PanBabinicz/ghost-feather/modules/sensor/bmi270/bmi270.h

#ifndef _BMI270_H
#define _BMI270_H

#include <stdint.h>

#ifdef __cplusplus
extern "C" {
#endif  /* __cplusplus */

///
/// \brief The BMI270 registers definition.
///
#define BMI270_REG_CHIP_ID                  (0x00)  /*!< Chip identification code.                          */
#define BMI270_REG_ERR_REG                  (0x02)  /*!< Reports sensor error condition.                    */
#define BMI270_REG_STATUS                   (0x03)  /*!< Sensor status flags.                               */
#define BMI270_REG_DATA_0                   (0x04)  /*!< AUX_X(LSB).                                        */
#define BMI270_REG_DATA_1                   (0x05)  /*!< AUX_X(MSB).                                        */
#define BMI270_REG_DATA_2                   (0x06)  /*!< AUX_Y(LSB).                                        */
#define BMI270_REG_DATA_3                   (0x07)  /*!< AUX_Y(MSB).                                        */
#define BMI270_REG_DATA_4                   (0x08)  /*!< AUX_Z(LSB).                                        */
#define BMI270_REG_DATA_5                   (0x09)  /*!< AUX_Z(MSB).                                        */
#define BMI270_REG_DATA_6                   (0x0a)  /*!< AUX_R(LSB).                                        */
#define BMI270_REG_DATA_7                   (0x0b)  /*!< AUX_R(MSB).                                        */
#define BMI270_REG_DATA_8                   (0x0c)  /*!< ACC_X(LSB).                                        */
#define BMI270_REG_DATA_9                   (0x0d)  /*!< ACC_X(MSB).                                        */
#define BMI270_REG_DATA_10                  (0x0e)  /*!< ACC_Y(LSB).                                        */
#define BMI270_REG_DATA_11                  (0x0f)  /*!< ACC_Y(MSB).                                        */
#define BMI270_REG_DATA_12                  (0x10)  /*!< ACC_Z(LSB).                                        */
#define BMI270_REG_DATA_13                  (0x11)  /*!< ACC_Z(MSB).                                        */
#define BMI270_REG_DATA_14                  (0x12)  /*!< GYR_X(LSB).                                        */
#define BMI270_REG_DATA_15                  (0x13)  /*!< GYR_X(MSB).                                        */
#define BMI270_REG_DATA_16                  (0x14)  /*!< GYR_Y(LSB).                                        */
#define BMI270_REG_DATA_17                  (0x15)  /*!< GYR_Y(MSB).                                        */
#define BMI270_REG_DATA_18                  (0x16)  /*!< GYR_Z(LSB).                                        */
#define BMI270_REG_DATA_19                  (0x17)  /*!< GYR_Z(MSB).                                        */
#define BMI270_REG_SENSORTIME_0             (0x18)  /*!< Sensor time <7:0>.                                 */
#define BMI270_REG_SENSORTIME_1             (0x19)  /*!< Sensor time <15:8>.                                */
#define BMI270_REG_SENSORTIME_2             (0x1a)  /*!< Sensor time <23:16>.                               */
#define BMI270_REG_EVENT                    (0x1b)  /*!< Sensor event flags.                                */
#define BMI270_REG_INT_STATUS_0             (0x1c)  /*!< Interrupt/Feature status.                          */
#define BMI270_REG_INT_STATUS_1             (0x1d)  /*!< Interrupt status 1.                                */
#define BMI270_REG_SC_OUT_0                 (0x1e)  /*!< Step counting value byte-0.                        */
#define BMI270_REG_SC_OUT_1                 (0x1f)  /*!< Step counting value byte-1.                        */
#define BMI270_REG_WR_GEST_ACT              (0x20)  /*!< Wrist gesture and activity detection output.       */
#define BMI270_REG_INST                     (0x21)  /*!< Error bits and messge indicating internal status.  */
#define BMI270_REG_TEMPERATURE_0            (0x22)  /*!< Temperature (LSB).                                 */
#define BMI270_REG_TEMPERATURE_1            (0x23)  /*!< Temperature (MSB).                                 */
#define BMI270_REG_FIFO_LENGTH_0            (0x24)  /*!< FIFO byte count register (LSB).                    */
#define BMI270_REG_FIFO_LENGTH_1            (0x25)  /*!< FIFO byte count register (MSB).                    */
#define BMI270_REG_FIFO_DATA                (0x26)  /*!< FIFO data output register.                         */
#define BMI270_REG_FEAT_PAGE                (0x2f)  /*!< Feature config/output page selector.               */
#define BMI270_REG_FEATURES_0               (0x30)  /*!< Input register for feature configuration.          */
#define BMI270_REG_FEATURES_1               (0x31)  /*!< Input register for feature configuration.          */
#define BMI270_REG_FEATURES_2               (0x32)  /*!< Input register for feature configuration.          */
#define BMI270_REG_FEATURES_3               (0x33)  /*!< Input register for feature configuration.          */
#define BMI270_REG_FEATURES_4               (0x34)  /*!< Input register for feature configuration.          */
#define BMI270_REG_FEATURES_5               (0x35)  /*!< Input register for feature configuration.          */
#define BMI270_REG_FEATURES_6               (0x36)  /*!< Input register for feature configuration.          */
#define BMI270_REG_FEATURES_7               (0x37)  /*!< Input register for feature configuration.          */
#define BMI270_REG_FEATURES_8               (0x38)  /*!< Input register for feature configuration.          */
#define BMI270_REG_FEATURES_9               (0x39)  /*!< Input register for feature configuration.          */
#define BMI270_REG_FEATURES_10              (0x3a)  /*!< Input register for feature configuration.          */
#define BMI270_REG_FEATURES_11              (0x3b)  /*!< Input register for feature configuration.          */
#define BMI270_REG_FEATURES_12              (0x3c)  /*!< Input register for feature configuration.          */
#define BMI270_REG_FEATURES_13              (0x3d)  /*!< Input register for feature configuration.          */
#define BMI270_REG_FEATURES_14              (0x3e)  /*!< Input register for feature configuration.          */
#define BMI270_REG_FEATURES_15              (0x3f)  /*!< Input register for feature configuration.          */
#define BMI270_REG_ACC_CONF                 (0x40)  /*!< Accelerometer ODR, bandwidth, mode config.         */
#define BMI270_REG_ACC_RANGE                (0x41)  /*!< Selection of the accelerometer g-range.            */
#define BMI270_REG_GYR_CONF                 (0x42)  /*!< Gyroscope ODR, bandwidth, mode config.             */
#define BMI270_REG_GYR_RANGE                (0x43)  /*!< Gyroscope angular rate measurement range.          */
#define BMI270_REG_AUX_CONF                 (0x44)  /*!< Auxiliary sensor interface ODR.                    */
#define BMI270_REG_FIFO_DOWNS               (0x45)  /*!< Gyroe and accel downsampling rates for FIFO.       */
#define BMI270_REG_FIFO_WTM_0               (0x46)  /*!< FIFO watermark level (LSB).                        */
#define BMI270_REG_FIFO_WTM_1               (0x47)  /*!< FIFO watermark level (MSB) and frame content conf. */
#define BMI270_REG_FIFO_CONFIG_0            (0x48)  /*!< FIFO frame content configuration.                  */
#define BMI270_REG_FIFO_CONFIG_1            (0x49)  /*!< FIFO frame content configuration.                  */
#define BMI270_REG_SATURATION               (0x4a)  /*!< Saturation information.                            */
#define BMI270_REG_AUX_DEV_ID               (0x4b)  /*!< Auxiliary interface device id.                     */
#define BMI270_REG_AUX_IF_CONF              (0x4c)  /*!< Auxiliary interface configuration register.        */
#define BMI270_REG_AUX_RD_ADDR              (0x4d)  /*!< Auxiliray interface read address.                  */
#define BMI270_REG_AUX_WR_ADDR              (0x4e)  /*!< Auxiliary include write address.                   */
#define BMI270_REG_AUX_WR_DATA              (0x4f)  /*!< Auxiliary include write data.                      */
#define BMI270_REG_ERR_REG_MSK              (0x52)  /*!< Error flag which triggers error interrupt.         */
#define BMI270_REG_INT1_IO_CTRL             (0x53)  /*!< Electrical behavior of the interrupt pin INT1.     */
#define BMI270_REG_INT2_IO_CTRL             (0x54)  /*!< Electrical behavior of the interrupt pin INT2.     */
#define BMI270_REG_INT_LATCH                (0x55)  /*!< Interrupt latch modes.                             */
#define BMI270_REG_INT1_MAP_FEAT            (0x56)  /*!< Interrupt/feature mapping on INT1.                 */
#define BMI270_REG_INT2_MAP_FEAT            (0x57)  /*!< Interrupt/feature mapping on INT2.                 */
#define BMI270_REG_INT_MAP_DATA             (0x58)  /*!< Data interrupt mapping for both INT pins.          */
#define BMI270_REG_INIT_CTRL                (0x59)  /*!< Start initialization.                              */
#define BMI270_REG_INIT_ADDR_0              (0x5b)  /*!< Base address of the initialization data.           */
#define BMI270_REG_INIT_ADDR_1              (0x5c)  /*!< Base address of the initialization data.           */
#define BMI270_REG_INIT_DATA                (0x5e)  /*!< Initialization register.                           */
#define BMI270_REG_INTERNAL_ERROR           (0x5f)  /*!< Internal error flags.                              */
#define BMI270_REG_AUX_IF_TRIM              (0x68)  /*!< Auxiliary interface trim register (NVM backend).   */
#define BMI270_REG_GYR_CRT_CONF             (0x69)  /*!< Component retrimming for gyroscope.                */
#define BMI270_REG_NVM_CONF                 (0x6a)  /*!< NVM configuration.                                 */
#define BMI270_REG_IF_CONF                  (0x6b)  /*!< Serial interface settings.                         */
#define BMI270_REG_DRV                      (0x6c)  /*!< Drive strenght control register (NVM backend).     */
#define BMI270_REG_ACC_SLF_TST              (0x6d)  /*!< Accelerometer self-test configuration and trigger. */
#define BMI270_REG_GYR_SLF_TST_AXES         (0x6e)  /*!< Gyro axes self-test configuration and trigger.     */
#define BMI270_REG_NV_CONF                  (0x70)  /*!< NVM backend configuration bits.                    */
#define BMI270_REG_OFFSET_0                 (0x71)  /*!< Offset compensation for accelerometer X-axis.      */
#define BMI270_REG_OFFSET_1                 (0x72)  /*!< Offset compensation for accelerometer Y-axis.      */
#define BMI270_REG_OFFSET_2                 (0x73)  /*!< Offset compensation for accelerometer Z-axis.      */
#define BMI270_REG_OFFSET_3                 (0x74)  /*!< Offset compensation for gyroscope X-axis.          */
#define BMI270_REG_OFFSET_4                 (0x75)  /*!< Offset compensation for gyroscope Y-axis.          */
#define BMI270_REG_OFFSET_5                 (0x76)  /*!< Offset compensation for gyroscope Z-axis.          */
#define BMI270_REG_OFFSET_6                 (0x77)  /*!< Offset copmensation (MSB gyroscope, enables).      */
#define BMI270_REG_PWR_CONF                 (0x7c)  /*!< Power mode configuration register.                 */
#define BMI270_REG_PWR_CTRL                 (0x7d)  /*!< Power mode control register.                       */
#define BMI270_REG_CMD                      (0x7e)  /*!< Command register.                                  */

///
/// \brief The BMI270 INST register fields.
///
#define BMI270_INST_MSK             (0xff << 0x00)  /*!< The internal status register mask.                 */
#define BMI270_INST_MSG_MSK         (0x0f << 0x00)  /*!< The internal status message mask.                  */
#define BMI270_INST_MSG_NOT_INIT    (0x00 << 0x00)  /*!< The internal status message ASIC is not init.      */
#define BMI270_INST_MSG_INIT_OK     (0x01 << 0x00)  /*!< The internal status message ASIC initialized.      */
#define BMI270_INST_MSG_INIT_ERR    (0x02 << 0x00)  /*!< The internal status message initialization error.  */
#define BMI270_INST_MSG_DRV_ERR     (0x03 << 0x00)  /*!< The internal status message invalid driver.        */
#define BMI270_INST_MSG_SNS_STOP    (0x04 << 0x00)  /*!< The internal status message sensor stop.           */
#define BMI270_INST_MSG_NVM_ERR     (0x05 << 0x00)  /*!< The internal status message NVM error.             */
#define BMI270_INST_MSG_START_ERR   (0x06 << 0x00)  /*!< The internal status message NVM and init error.    */
#define BMI270_INST_MSG_COMPAT_ERR  (0x07 << 0x00)  /*!< The internal status message compatibility error.   */
#define BMI270_INST_AXES_REMAP      (0x01 << 0x05)  /*!< The internal status incorrect axes remapping.      */
#define BMI270_INST_ODR_50HZ_ERR    (0x01 << 0x06)  /*!< The internal status minimum bandwidth are not met. */

///
/// \brief The BMI270 GYR_GAIN_STATUS register fields.
///
#define BMI270_GYR_GAIN_STAT_MSK    (0x3f << 0x00)  /*!< Describes the saturation status for the gyro gain. */
#define BMI270_GYR_GAIN_STAT_SAT_X  (0x01 << 0x00)  /*!< Gain results to saturated value for x axis.        */
#define BMI270_GYR_GAIN_STAT_SAT_Y  (0x01 << 0x01)  /*!< Gain results to saturated value for y axis.        */
#define BMI270_GYR_GAIN_STAT_SAT_Z  (0x01 << 0x02)  /*!< Gain results to saturated value for z axis.        */
#define BMI270_GYR_GAIN_STAT_NO_ERR (0x00 << 0x03)  /*!< Selected feature has been executed.                */
#define BMI270_GYR_GAIN_STAT_PRECON (0x01 << 0x03)  /*!< Precondition to start the feature was not ended.   */
#define BMI270_GYR_GAIN_STAT_DL     (0x02 << 0x03)  /*!< Unsuccessful download of 2kB configuration stream. */
#define BMI270_GYR_GAIN_STAT_ABORT  (0x03 << 0x03)  /*!< Command is aborted.                                */

///
/// \brief The BMI270 ACC_CONF register fields.
///
#define BMI270_ACC_MSK              (0xff << 0x00)  /*!< The accelerometer mask.                            */
#define BMI270_ACC_ODR_MSK          (0x0f << 0x00)  /*!< The accelerometer ODR mask.                        */
#define BMI270_ACC_ODR_0P78         (0x01 << 0x00)  /*!< The accelerometer ODR equal to 25/32 Hz.           */
#define BMI270_ACC_ODR_1P5          (0x02 << 0x00)  /*!< The accelerometer ODR equal to 25/16 Hz.           */
#define BMI270_ACC_ODR_3P1          (0x03 << 0x00)  /*!< The accelerometer ODR equal to 25/8  Hz.           */
#define BMI270_ACC_ODR_6P25         (0x04 << 0x00)  /*!< The accelerometer ODR equal to 25/4  Hz.           */
#define BMI270_ACC_ODR_12P5         (0x05 << 0x00)  /*!< The accelerometer ODR equal to 25/2  Hz.           */
#define BMI270_ACC_ODR_25           (0x06 << 0x00)  /*!< The accelerometer ODR equal to 25    Hz.           */
#define BMI270_ACC_ODR_50           (0x07 << 0x00)  /*!< The accelerometer ODR equal to 50    Hz.           */
#define BMI270_ACC_ODR_100          (0x08 << 0x00)  /*!< The accelerometer ODR equal to 100   Hz.           */
#define BMI270_ACC_ODR_200          (0x09 << 0x00)  /*!< The accelerometer ODR equal to 200   Hz.           */
#define BMI270_ACC_ODR_400          (0x0a << 0x00)  /*!< The accelerometer ODR equal to 400   Hz.           */
#define BMI270_ACC_ODR_800          (0x0b << 0x00)  /*!< The accelerometer ODR equal to 800   Hz.           */
#define BMI270_ACC_ODR_1k6          (0x0c << 0x00)  /*!< The accelerometer ODR equal to 1600  Hz.           */
#define BMI270_ACC_ODR_3k2          (0x0d << 0x00)  /*!< Reserved.                                          */
#define BMI270_ACC_ODR_6k4          (0x0e << 0x00)  /*!< Reserved.                                          */
#define BMI270_ACC_ODR_12k8         (0x0f << 0x00)  /*!< Reserved.                                          */
#define BMI270_ACC_BWP_MSK          (0x07 << 0x04)  /*!< The accelerometer bandwidth mask.                  */
#define BMI270_ACC_BWP_OSR4_AVG1    (0x00 << 0x04)  /*!< The accelerometer OSR4 mode / no averaging.        */
#define BMI270_ACC_BWP_OSR2_AVG2    (0x01 << 0x04)  /*!< The accelerometer OSR2 mode / average 2 samples.   */
#define BMI270_ACC_BWP_NORM_AVG4    (0x02 << 0x04)  /*!< The accelerometer normal mode / average 4 samples. */
#define BMI270_ACC_BWP_CIC_AVG8     (0x03 << 0x04)  /*!< The accelerometer CIC mode / average 8 samples.    */
#define BMI270_ACC_BWP_RES_AVG16    (0x04 << 0x04)  /*!< Reserved mode / average 16 samples.                */
#define BMI270_ACC_BWP_RES_AVG32    (0x05 << 0x04)  /*!< Reserved mode / average 32 samples.                */
#define BMI270_ACC_BWP_RES_AVG64    (0x06 << 0x04)  /*!< Reserved mode / average 64 samples.                */
#define BMI270_ACC_BWP_RES_AVG128   (0x07 << 0x04)  /*!< Reserved mode / average 128 samples.               */
#define BMI270_ACC_FILT_PERF_MSK    (0x01 << 0x07)  /*!< The accelerometer filter perfromance mask.         */
#define BMI270_ACC_FILT_PERF_ULP    (0x00 << 0x07)  /*!< The accelerometer filter power optimized mode.     */
#define BMI270_ACC_FILT_PERF_HP     (0x01 << 0x07)  /*!< The accelerometer filter perf optimized mode.      */

///
/// \brief The BMI270 ACC_RANGE register g-range field.
///
#define BMI270_ACC_RANGE_MSK        (0x03 << 0x00)  /*!< The accelerometer g-range mask.                    */
#define BMI270_ACC_RANGE_2G         (0x00 << 0x00)  /*!< The accelerometer g-range +/-2g.                   */
#define BMI270_ACC_RANGE_4G         (0x01 << 0x00)  /*!< The accelerometer g-range +/-4g.                   */
#define BMI270_ACC_RANGE_8G         (0x02 << 0x00)  /*!< The accelerometer g-range +/-8g.                   */
#define BMI270_ACC_RANGE_16G        (0x03 << 0x00)  /*!< The accelerometer g-range +/-16g.                  */

///
/// \brief The BMI270 GYR_CONF register fields.
///
#define BMI270_GYR_MSK              (0xff << 0x00)  /*!< The gyroscope mask.                                */
#define BMI270_GYR_ODR_MSK          (0x0f << 0x00)  /*!< The gyroscope ODR mask.                            */
#define BMI270_GYR_ODR_0P78         (0x01 << 0x00)  /*!< Reserved.                                          */
#define BMI270_GYR_ODR_1P5          (0x02 << 0x00)  /*!< Reserved.                                          */
#define BMI270_GYR_ODR_3P1          (0x03 << 0x00)  /*!< Reserved.                                          */
#define BMI270_GYR_ODR_6P25         (0x04 << 0x00)  /*!< Reserved.                                          */
#define BMI270_GYR_ODR_12P5         (0x05 << 0x00)  /*!< Reserved.                                          */
#define BMI270_GYR_ODR_25           (0x06 << 0x00)  /*!< The gyroscope ODR equal to 25    Hz.               */
#define BMI270_GYR_ODR_50           (0x07 << 0x00)  /*!< The gyroscope ODR equal to 50    Hz.               */
#define BMI270_GYR_ODR_100          (0x08 << 0x00)  /*!< The gyroscope ODR equal to 100   Hz.               */
#define BMI270_GYR_ODR_200          (0x09 << 0x00)  /*!< The gyroscope ODR equal to 200   Hz.               */
#define BMI270_GYR_ODR_400          (0x0a << 0x00)  /*!< The gyroscope ODR equal to 400   Hz.               */
#define BMI270_GYR_ODR_800          (0x0b << 0x00)  /*!< The gyroscope ODR equal to 800   Hz.               */
#define BMI270_GYR_ODR_1k6          (0x0c << 0x00)  /*!< The gyroscope ODR equal to 1600  Hz.               */
#define BMI270_GYR_ODR_3k2          (0x0d << 0x00)  /*!< The gyroscope ODR equal to 3200  HZ.               */
#define BMI270_GYR_ODR_6k4          (0x0e << 0x00)  /*!< Reserved.                                          */
#define BMI270_GYR_ODR_12k8         (0x0f << 0x00)  /*!< Reserved.                                          */
#define BMI270_GYR_BWP_MSK          (0x03 << 0x04)  /*!< The gyroscope bandwidth mask.                      */
#define BMI270_GYR_BWP_OSR4         (0x00 << 0x04)  /*!< The gyroscope OSR4 mode.                           */
#define BMI270_GYR_BWP_OSR2         (0x01 << 0x04)  /*!< The gyroscope OSR2 mode.                           */
#define BMI270_GYR_BWP_NORM         (0x02 << 0x04)  /*!< The gyroscope normal mode.                         */
#define BMI270_GYR_BWP_RES          (0x03 << 0x04)  /*!< Reserved.                                          */
#define BMI270_GYR_NOISE_PERF_MSK   (0x01 << 0x06)  /*!< The gyroscope noise performance mask.              */
#define BMI270_GYR_NOISE_PERF_ULP   (0x00 << 0x06)  /*!< The gyroscope noise power optimized mode.          */
#define BMI270_GYR_NOISE_PERF_HP    (0x01 << 0x06)  /*!< The gyroscope noise perf optimized mode.           */
#define BMI270_GYR_FILT_PERF_MSK    (0x01 << 0x07)  /*!< The gyroscope filter performance mask.             */
#define BMI270_GYR_FILT_PERF_ULP    (0x00 << 0x07)  /*!< The gyroscope filter power optimized mode.         */
#define BMI270_GYR_FILT_PERF_HP     (0x01 << 0x07)  /*!< The gyroscope filter perf optimized mode.          */

///
/// \brief The BMI270 GYR_RANGE register fields.
///
#define BMI270_GYR_RANGE_MSK        (0x07 << 0x00)  /*!< The gyroscope range mask.                          */
#define BMI270_GYR_RANGE_2000       (0x00 << 0x00)  /*!< The gyroscope range +/-2000dps, 16.4  LSB/dps.     */
#define BMI270_GYR_RANGE_1000       (0x01 << 0x00)  /*!< The gyroscope range +/-1000dps, 32.8  LSB/dps.     */
#define BMI270_GYR_RANGE_500        (0x02 << 0x00)  /*!< The gyroscope range +/-500 dps, 65.6  LSB/dps.     */
#define BMI270_GYR_RANGE_250        (0x03 << 0x00)  /*!< The gyroscope range +/-250 dps, 131.2 LSB/dps.     */
#define BMI270_GYR_RANGE_125        (0x04 << 0x00)  /*!< The gyroscope range +/-125 dps, 262.4 LSB/dps.     */
#define BMI270_GYR_OIS_MSK          (0x01 << 0x03)  /*!< The gyroscope ois range mask.                      */
#define BMI270_GYR_OIS_250          (0x00 << 0x03)  /*!< The gyroscope ois +/-250dps,  131.2 LSB/dps.       */
#define BMI270_GYR_OIS_2000         (0x01 << 0x03)  /*!< The gyroscope ois +/-2000dps, 16.4  LSB/dps.       */

///
/// \brief The BMI270 ACC_SELF_TEST register fields.
///
#define BMI270_ACC_SLF_TST_MSK      (0x0f << 0x00)  /*!< The accelerometer self-test configuration mask.    */
#define BMI270_ACC_SLF_TST_EN_OFF   (0x00 << 0x00)  /*!< Disable accelerometer self-test.                   */
#define BMI270_ACC_SLF_TST_EN_ON    (0x01 << 0x00)  /*!< Enable accelerometer self-test.                    */
#define BMI270_ACC_SLF_TST_SIG_NEG  (0x00 << 0x02)  /*!< Set the self-test sign to negative.                */
#define BMI270_ACC_SLF_TST_SIG_POS  (0x01 << 0x02)  /*!< Set the self-test sign to possitive.               */
#define BMI270_ACC_SLF_TST_AMP_LOW  (0x00 << 0x03)  /*!< Set amplitude of the self-test deflection to low.  */
#define BMI270_ACC_SLF_TST_AMP_HIGH (0x01 << 0x03)  /*!< Set amplitude of the self-test deflection to high. */

///
/// \brief The BMI270 ACC_SELF_TEST register fields.
///
#define BMI270_GYR_SLF_TST_MSK      (0x0f << 0x00)  /*!< The gyroscope self-test configuration mask.        */
#define BMI270_GYR_SLF_TST_DONE_MSK (0x01 << 0x00)  /*!< Gyroscope functional test of detection ended mask. */
#define BMI270_GYR_SLF_TST_DONE     (0x01 << 0x00)  /*!< Gyroscope functional test of detection ended.      */
#define BMI270_GYR_SLF_TST_X_MSK    (0x00 << 0x03)  /*!< Gyroscope X-axis self test mask.                   */
#define BMI270_GYR_SLF_TST_X_ERR    (0x00 << 0x01)  /*!< Error status of gyro X-axis self test.             */
#define BMI270_GYR_SLF_TST_X_OK     (0x01 << 0x01)  /*!< OK status of gyro X-axis self test.                */
#define BMI270_GYR_SLF_TST_Y_MSK    (0x00 << 0x03)  /*!< Gyroscope Y-axis self test mask.                   */
#define BMI270_GYR_SLF_TST_Y_ERR    (0x00 << 0x02)  /*!< Error status of gyro Y-axis self test.             */
#define BMI270_GYR_SLF_TST_Y_OK     (0x01 << 0x02)  /*!< OK status of gyro Y-axis self test.                */
#define BMI270_GYR_SLF_TST_Z_MSK    (0x00 << 0x03)  /*!< Gyroscope Z-axis self test mask.                   */
#define BMI270_GYR_SLF_TST_Z_ERR    (0x00 << 0x03)  /*!< Error status of gyro Z-axis self test.             */
#define BMI270_GYR_SLF_TST_Z_OK     (0x01 << 0x03)  /*!< OK status of gyro Z-axis self test.                */

///
/// \brief The BMI270 PWR_CONF register fields.
///
#define BMI270_PWR_CONF_MSK         (0x07 << 0x00)  /*!< The power conf mask.                               */
#define BMI270_PWR_CONF_APS_MSK     (0x01 << 0x00)  /*!< The power conf advanced power save mask.           */
#define BMI270_PWR_CONF_APS_OFF     (0x00 << 0x00)  /*!< The advanced power save off.                       */
#define BMI270_PWR_CONF_APS_ON      (0x01 << 0x00)  /*!< The advanced power save on.                        */
#define BMI270_PWR_CONF_FSW_MSK     (0x01 << 0x01)  /*!< The power conf FIFO read disable in lp mode mask.  */
#define BMI270_PWR_CONF_FSW_OFF     (0x00 << 0x01)  /*!< The FIFO read disabled in lp mode.                 */
#define BMI270_PWR_CONF_FSW_ON      (0x01 << 0x01)  /*!< The FIFO read enabled in lp mode after FIFO int.   */
#define BMI270_PWR_CONF_FUP_MSK     (0x01 << 0x02)  /*!< The fast power up enabled mask.                    */
#define BMI270_PWR_CONF_FUP_OFF     (0x00 << 0x02)  /*!< The fast power up disabled.                        */
#define BMI270_PWR_CONF_FUP_ON      (0x01 << 0x02)  /*!< The fast power up enabled.                         */

///
/// \brief The BMI270 PWR_CONF register fields.
///
#define BMI270_INIT_CTRL_MSK        (0xff << 0x00)  /*!< The bmi270 init control mask.                      */
#define BMI270_INIT_CTRL_START      (0x00 << 0x00)  /*!< The bmi270 init control start.                     */

///
/// \brief The BMI270 PWR_CTRL register fields.
///
#define BMI270_PWR_CTRL_MSK         (0x0f << 0x00)  /*!< The bmi270 power control mask.                     */
#define BMI270_PWR_CTRL_AUX_MSK     (0x01 << 0x00)  /*!< The bmi270 power control auxiliary sensor mask.    */
#define BMI270_PWR_CTRL_AUX_OFF     (0x00 << 0x00)  /*!< The auxiliary sensor off.                          */
#define BMI270_PWR_CTRL_AUX_ON      (0x01 << 0x00)  /*!< The auxiliary sensor on.                           */
#define BMI270_PWR_CTRL_GYR_MSK     (0x01 << 0x01)  /*!< The bmi270 power control gyroscope mask.           */
#define BMI270_PWR_CTRL_GYR_OFF     (0x00 << 0x01)  /*!< The gyroscope off.                                 */
#define BMI270_PWR_CTRL_GYR_ON      (0x01 << 0x01)  /*!< The gyroscope on.                                  */
#define BMI270_PWR_CTRL_ACC_MSK     (0x01 << 0x02)  /*!< The bmi270 power control accelerometer mask.       */
#define BMI270_PWR_CTRL_ACC_OFF     (0x00 << 0x02)  /*!< The accelerometer off.                             */
#define BMI270_PWR_CTRL_ACC_ON      (0x01 << 0x02)  /*!< The accelerometer on.                              */
#define BMI270_PWR_CTRL_TEMP_MSK    (0x01 << 0x03)  /*!< The bmi270 power control temperature sensor mask.  */
#define BMI270_PWR_CTRL_TEMP_OFF    (0x00 << 0x03)  /*!< The temperature sensor off.                        */
#define BMI270_PWR_CTRL_TEMP_ON     (0x01 << 0x03)  /*!< The temperature sensor on.                         */

///
/// \brief The BMI270 CMD register fields.
///
#define BMI270_CMD_MSK              (0xff << 0x00)  /*!< The bmi270 cmd mask.                               */
#define BMI270_CMD_G_TRIGGER        (0x02 << 0x00)  /*!< The cmd which triggers special gyro ops.           */
#define BMI270_CMD_USR_GAIN         (0x03 << 0x00)  /*!< The cmd which applies new gyro gain value.         */
#define BMI270_CMD_NVM_PROG         (0xa0 << 0x00)  /*!< The cmd which writes the NVM backed reg into NVM.  */
#define BMI270_CMD_FIFO_FLUSH       (0xb0 << 0x00)  /*!< The cmd which clears FIFO content.                 */
#define BMI270_CMD_SOFTRESET        (0xb6 << 0x00)  /*!< The cmd which triggers a reset.                    */

///
/// \brief The BMI270 register values at POR.
///
#define BMI270_POR_CHIP_ID          (0x24)          /*!< The bmi270 chip id value at POR.                   */
#define BMI270_POR_PWR_CONF         (0x03)          /*!< The bmi270 power configuration value at POR.       */

///
/// \brief The BMI270 device type.
///
struct bmi270_dev;

///
/// \brief The BMI270 power mode configuration type.
///
struct bmi270_pwr_mode_conf;

///
/// \brief The BMI270 result type.
///
typedef enum bmi270_res
{
    BMI270_RES_BEGIN = 0,
    BMI270_RES_OK    = 0,
    BMI270_RES_ERR,
    BMI270_RES_VLD_ERR,
    BMI270_RES_TOTAL,
} bmi270_res_t;

///
/// \brief The BMI270 status type.
///
typedef enum bmi270_stat
{
    BMI270_STAT_BEGIN  = 0,
    BMI270_STAT_DEINIT = 0,
    BMI270_STAT_INIT,
    BMI270_STAT_TOTAL,
} bmi270_stat_t;

///
/// \brief The BMI270 power mode type.
///
typedef enum bmi270_pwr_mode
{
    BMI270_PWR_MODE_BEGIN = 0,
    BMI270_PWR_MODE_SUSP  = 0,
    BMI270_PWR_MODE_CONF,
    BMI270_PWR_MODE_LOW_ACC_ONLY,
    BMI270_PWR_MODE_LOW_GYR_ONLY,
    BMI270_PWR_MODE_LOW_IMU,
    BMI270_PWR_MODE_NORM_ACC_ONLY,
    BMI270_PWR_MODE_NORM_GYR_ONLY,
    BMI270_PWR_MODE_NORM_IMU,
    BMI270_PWR_MODE_PERF_ACC_ONLY,
    BMI270_PWR_MODE_PERF_GYR_ONLY,
    BMI270_PWR_MODE_PERF_IMU,
    BMI270_PWR_MODE_TOTAL,
} bmi270_pwr_mode_t;

///
/// \brief Gets the BMI270 device.
///
/// \return struct bmi270_dev* The BMI270 device address.
///
struct bmi270_dev* bmi270_dev_get(void);

///
/// \brief Gets the BMI270 power mode config.
///
/// \param[in] pwr_mode The selected power mode.
///
/// \return bmi270_pwr_mode_conf_t The power mode config.
///
const struct bmi270_pwr_mode_conf* bmi270_pwr_mode_get_conf(const bmi270_pwr_mode_t pwr_mode);

///
/// \brief Initializes the BMI270.
///
/// \param[in] dev The BMI270 device.
///
/// \return bmi270_res_t   The BMI270 result.
/// \retval BMI270_RES_OK  On success.
/// \retval BMI270_RES_ERR Otherwise.
///
bmi270_res_t bmi270_init(void);

///
/// \brief Deinitializes the BMI270.
///
/// \param[in] dev The BMI270 device.
///
void bmi270_deinit(void);

///
/// \brief Performs soft reset of the BMI270.
///
/// \note  After every POR or soft reset, the IMU remains in suspend mode. To get ready for
///        operation the device must be initialized through init procedure.
///
void bmi270_soft_rst(void);

///
/// \brief Sets the power mode.
///
/// \param[in] pwr_mode_conf The pointer to power mode config.
///
void bmi270_pwr_mode_set(bmi270_pwr_mode_t pwr_mode);

///
/// \brief Sets the device status.
///
/// \param[in] stat The BMI270 device status.
///
void bmi270_stat_set(const bmi270_stat_t stat);

///
/// \brief Gets the device status.
///
/// \return bmi270_stat_t      The BMI270 status.
/// \retval BMI270_STAT_DEINIT When deinitialized.
/// \retval BMI270_STAT_INIT   When initialized.
///
bmi270_stat_t bmi270_stat_get(void);

///
/// \brief Self-tests accelerometer.
///
/// \return bmi270_res_t   The BMI270 result.
/// \retval BMI270_RES_OK  On success.
/// \retval BMI270_RES_ERR Otherwise.
///
bmi270_res_t bmi270_acc_slf_tst(void);

///
/// \brief Self-tests gyroscope.
///
/// \return bmi270_res_t   The BMI270 result.
/// \retval BMI270_RES_OK  On success.
/// \retval BMI270_RES_ERR Otherwise.
///
bmi270_res_t bmi270_gyr_slf_tst(void);

///
/// \brief Reads the accelerometer data.
///
void bmi270_acc_read(void);

///
/// \brief Gets the accelerometer x axis value.
///
/// \return int16_t The accelerometer value on x-axis.
///
int16_t bmi270_acc_get_x(void);

///
/// \brief Sets the accelerometer x axis value.
///
/// \param[in] x The x-axis value.
///
void bmi270_acc_set_x(const int16_t x);

///
/// \brief Gets the accelerometer y axis value.
///
/// \return int16_t The accelerometer value on y-axis.
///
int16_t bmi270_acc_get_y(void);

///
/// \brief Sets the accelerometer y axis value.
///
/// \param[in] y The y-axis value.
///
void bmi270_acc_set_y(const int16_t y);

///
/// \brief Gets the accelerometer z axis value.
///
/// \return int16_t The accelerometer value on z-axis.
///
int16_t bmi270_acc_get_z(void);

///
/// \brief Sets the accelerometer z axis value.
///
/// \param[in] z The z-axis value.
///
void bmi270_acc_set_z(const int16_t z);

///
/// \brief Reads the gyroscope data.
///
void bmi270_gyr_read(void);

///
/// \brief Gets the gyroscope x axis value.
///
/// \return int16_t The gyroscope value on x-axis.
///
int16_t bmi270_gyr_get_x(void);

///
/// \brief Sets the gyroscope x axis value.
///
/// \param[in] x The x-axis value.
///
void bmi270_gyr_set_x(const int16_t x);

///
/// \brief Gets the gyroscope y axis value.
///
/// \return int16_t The gyroscope value on y-axis.
///
int16_t bmi270_gyr_get_y(void);

///
/// \brief Sets the gyroscope y axis value.
///
/// \param[in] y The y-axis value.
///
void bmi270_gyr_set_y(const int16_t y);

///
/// \brief Gets the gyroscope z axis value.
///
/// \return int16_t The gyroscope value on z-axis.
///
int16_t bmi270_gyr_get_z(void);

///
/// \brief Sets the gyroscope z axis value.
///
/// \param[in] z The z-axis value.
///
void bmi270_gyr_set_z(const int16_t z);

///
/// \brief Reads the temperature data.
///
void bmi270_temp_read(void);

///
/// \brief Gets the temperature value.
///
/// \return int16_t The temperature value.
///
int16_t bmi270_temp_get(void);

///
/// \brief Sets the temperature value.
///
/// \param[in] temp The temperature value.
///
void bmi270_temp_set(int16_t temp);

///
/// \brief Reads the sensor time register data.
///
void bmi270_time_read(void);

///
/// \brief Gets the sensor time value.
///
/// \return uint32_t The sensor time value.
///
uint32_t bmi270_time_get(void);

///
/// \brief Sets the sensor time value.
///
/// \param[in] time The sensor time value.
///
void bmi270_time_set(const uint32_t time);

#ifdef __cplusplus
}
#endif  /* __cplusplus */

#endif  /* _BMI270_H */
