PanBabinicz/ghost-feather/modules/tim/tim.c

#include "tim.h"
#include "ll_tim_advx.h"
#include "ll_tim_common.h"
#include "ll_tim_gpx.h"

///***********************************************************************************************************
/// Private objects - definition.
///***********************************************************************************************************
///
/// \brief The TIM4 device.
///
static struct ll_tim_gpx_tim2345_dev tim4 =
{
    .rmap = (volatile struct ll_tim_gpx_tim2345_regs *)(0x40000800),
    .rtmp =
    {
        .cr1 =
        {
            .bf =
            {
                .cen      = 0x00,
                .udis     = 0x00,
                .urs      = 0x00,
                .opm      = 0x00,
                .dir      = 0x00,
                .cms      = 0x00,
                .arpe     = 0x00,
                .ckd      = 0x00,
                .uifremap = 0x00,
            },
        },

        .cr2 =
        {
            .bf =
            {
                .ccds = 0x00,
                .mms  = 0x00,
                .ti1s = 0x00,
            },
        },

        .smcr =
        {
            .bf =
            {
                .sms     = 0x00,
                .occs    = 0x00,
                .ts      = 0x00,
                .msm     = 0x00,
                .etf     = 0x00,
                .etps    = 0x00,
                .ece     = 0x00,
                .etp     = 0x00,
                .sms_msb = 0x00,
            },
        },

        .dier =
        {
            .bf =
            {
                .uie   = 0x00,
                .cc1ie = 0x00,
                .cc2ie = 0x00,
                .cc3ie = 0x00,
                .cc4ie = 0x00,
                .tie   = 0x00,
                .ude   = 0x00,
                .cc1de = 0x00,
                .cc2de = 0x00,
                .cc3de = 0x00,
                .cc4de = 0x00,
                .tde   = 0x00,
            },
        },

        .sr =
        {
            .bf =
            {
                .uif   = 0x00,
                .cc1if = 0x00,
                .cc2if = 0x00,
                .cc3if = 0x00,
                .cc4if = 0x00,
                .tif   = 0x00,
                .cc1of = 0x00,
                .cc2of = 0x00,
                .cc3of = 0x00,
                .cc4of = 0x00,
            },
        },

        .egr =
        {
            .bf =
            {
                .ug   = 0x00,
                .cc1g = 0x00,
                .cc2g = 0x00,
                .cc3g = 0x00,
                .cc4g = 0x00,
                .tg   = 0x00,
            },
        },

        .ccmr1 =
        {
            .out =
            {
                .bf =
                {
                    .cc1s     = 0x00,
                    .oc1fe    = 0x00,
                    .oc1pe    = 0x00,
                    .oc1m     = LL_TIM_GPX_TIM2345_OC_MODE_PWM1,
                    .oc1ce    = 0x00,
                    .cc2s     = 0x00,
                    .oc2fe    = 0x00,
                    .oc2pe    = 0x00,
                    .oc2m     = LL_TIM_GPX_TIM2345_OC_MODE_PWM1,
                    .oc2ce    = 0x00,
                    .oc1m_msb = 0x00,
                    .oc2m_msb = 0x00,
                },
            },
        },

        .ccmr2 =
        {
            .out =
            {
                .bf =
                {
                    .cc3s     = 0x00,
                    .oc3fe    = 0x00,
                    .oc3pe    = 0x00,
                    .oc3m     = LL_TIM_GPX_TIM2345_OC_MODE_PWM1,
                    .oc3ce    = 0x00,
                    .cc4s     = 0x00,
                    .oc4fe    = 0x00,
                    .oc4pe    = 0x00,
                    .oc4m     = LL_TIM_GPX_TIM2345_OC_MODE_PWM1,
                    .oc4ce    = 0x00,
                    .oc3m_msb = 0x00,
                    .oc4m_msb = 0x00,
                },
            },
        },

        .ccer =
        {
            .bf =
            {
                .cc1e  = 0x01,
                .cc1p  = 0x00,
                .cc1np = 0x00,
                .cc2e  = 0x01,
                .cc2p  = 0x00,
                .cc2np = 0x00,
                .cc3e  = 0x01,
                .cc3p  = 0x00,
                .cc3np = 0x00,
                .cc4e  = 0x01,
                .cc4p  = 0x00,
                .cc4np = 0x00,
            },
        },

        .cnt =
        {
            .bf =
            {
                .cnt    = 0x00,
                .uifcpy = 0x00,
            },
        },

        .psc =
        {
            .bf =
            {
                .psc = 0x6b,
            },
        },

        .arr =
        {
            .bf =
            {
                .arr = 0x4844,
            },
        },

        .ccr1 =
        {
            .bf =
            {
                .ccr1 = 0x05dc,
            },
        },

        .ccr2 =
        {
            .bf =
            {
                .ccr2 = 0x05dc,
            },
        },

        .ccr3 =
        {
            .bf =
            {
                .ccr3 = 0x05dc,
            },
        },

        .ccr4 =
        {
            .bf =
            {
                .ccr4 = 0x05dc,
            },
        },

        .dcr =
        {
            .bf =
            {
                .dba = 0x00,
                .dbl = 0x00,
            },
        },

        .dmar =
        {
            .bf =
            {
                .dmab = 0x00,
            },
        },

        .tim2_or =
        {
            .bf =
            {
                .itr1_rmp = 0x00,
            },
        },

        .tim5_or =
        {
            .bf =
            {
                .ti4_rmp = 0x00,
            },
        },
    },
    .ccr_data   = { 0 },
    .id         = LL_TIM_GPX_TIM2345_ID_4,
    .ccmr1_mode = LL_TIM_GPX_TIM2345_MODE_OUT_COMP,
    .ccmr2_mode = LL_TIM_GPX_TIM2345_MODE_OUT_COMP,
    .stat       = false,
};

///
/// \brief The TIM12 device.
///
static struct ll_tim_gpx_tim912_dev tim12 =
{
    .rmap = (volatile struct ll_tim_gpx_tim912_regs *)(0x40001800),
    .rtmp =
    {
        .cr1 =
        {
            .bf =
            {
                .cen      = 0x00,
                .udis     = 0x00,
                .urs      = 0x00,
                .opm      = 0x00,
                .arpe     = 0x00,
                .ckd      = 0x00,
                .uifremap = 0x00,
            },
        },

        .smcr =
        {
            .bf =
            {
                .sms     = 0x00,
                .ts      = 0x00,
                .msm     = 0x00,
                .sms_msb = 0x00,
            },
        },

        .dier =
        {
            .bf =
            {
                .uie   = 0x00,
                .cc1ie = 0x01,
                .cc2ie = 0x01,
                .tie   = 0x00,
            },
        },

        .sr =
        {
            .bf =
            {
                .uif   = 0x00,
                .cc1if = 0x00,
                .cc2if = 0x00,
                .tif   = 0x00,
                .cc1of = 0x00,
                .cc2of = 0x00,
            },
        },

        .egr =
        {
            .bf =
            {
                .ug   = 0x00,
                .cc1g = 0x00,
                .cc2g = 0x00,
                .tg   = 0x00,
            },
        },

        .ccmr1 =
        {
            .in =
            {
                .bf =
                {
                    .cc1s   = 0x01,
                    .ic1psc = 0x00,
                    .ic1f   = 0x00,
                    .cc2s   = 0x01,
                    .ic2psc = 0x00,
                    .ic2f   = 0x00,
                },
            },
        },

        .ccer =
        {
            .bf =
            {
                .cc1e  = 0x01,
                .cc1p  = 0x01,
                .cc1np = 0x01,
                .cc2e  = 0x01,
                .cc2p  = 0x01,
                .cc2np = 0x01,
            },
        },

        .cnt =
        {
            .bf =
            {
                .cnt    = 0x00,
                .uifcpy = 0x00,
            },
        },

        .psc =
        {
            .bf =
            {
                .psc = 0x6b,
            },
        },

        .arr =
        {
            .bf =
            {
                .arr = 0xffff,
            },
        },

        .ccr1 =
        {
            .bf =
            {
                .ccr1 = 0x00,
            },
        },

        .ccr2 =
        {
            .bf =
            {
                .ccr2 = 0x00,
            },
        },
    },
    .ccr_data   = { 0 },
    .id         = LL_TIM_GPX_TIM912_ID_12,
    .ccmr1_mode = LL_TIM_GPX_TIM912_MODE_IN_CAP,
    .stat       = false,
};

///
/// \brief The TIM8 device.
///
static struct ll_tim_adv6_tim18_dev tim8 =
{
    .rmap = (volatile struct ll_tim_adv6_tim18_regs *)(0x40010400),
    .rtmp =
    {
        .cr1 =
        {
            .bf =
            {
                .cen      = 0x00,
                .udis     = 0x00,
                .urs      = 0x00,
                .opm      = 0x00,
                .dir      = 0x00,
                .cms      = 0x00,
                .arpe     = 0x00,
                .ckd      = 0x00,
                .uifremap = 0x00,
            },
        },

        .cr2 =
        {
            .bf =
            {
                .ccpc  = 0x00,
                .ccus  = 0x00,
                .ccds  = 0x00,
                .mms   = 0x00,
                .ti1s  = 0x00,
                .ois1  = 0x00,
                .ois1n = 0x00,
                .ois2  = 0x00,
                .ois2n = 0x00,
                .ois3  = 0x00,
                .ois3n = 0x00,
                .ois4  = 0x00,
                .ois5  = 0x00,
                .ois6  = 0x00,
                .mms2  = 0x00,
            },
        },

        .smcr =
        {
            .bf =
            {
                .sms     = 0x00,
                .ts      = 0x00,
                .msm     = 0x00,
                .etf     = 0x00,
                .etps    = 0x00,
                .ece     = 0x00,
                .etp     = 0x00,
                .sms_msb = 0x00,
            },
        },

        .dier =
        {
            .bf =
            {
                .uie   = 0x00,
                .cc1ie = 0x01,
                .cc2ie = 0x01,
                .cc3ie = 0x01,
                .cc4ie = 0x01,
                .comie = 0x00,
                .tie   = 0x00,
                .bie   = 0x00,
                .ude   = 0x00,
                .cc1de = 0x00,
                .cc2de = 0x00,
                .cc3de = 0x00,
                .cc4de = 0x00,
                .comde = 0x00,
                .tde   = 0x00,
            },
        },

        .sr =
        {
            .bf =
            {
                .uif   = 0x00,
                .cc1if = 0x00,
                .cc2if = 0x00,
                .cc3if = 0x00,
                .cc4if = 0x00,
                .comif = 0x00,
                .tif   = 0x00,
                .bif   = 0x00,
                .b2if  = 0x00,
                .cc1of = 0x00,
                .cc2of = 0x00,
                .cc3of = 0x00,
                .cc4of = 0x00,
                .cc5if = 0x00,
                .cc6if = 0x00,
            },
        },

        .egr =
        {
            .bf =
            {
                .ug   = 0x00,
                .cc1g = 0x00,
                .cc2g = 0x00,
                .cc3g = 0x00,
                .cc4g = 0x00,
                .comg = 0x00,
                .tg   = 0x00,
                .bg   = 0x00,
                .b2g  = 0x00,
            },
        },

        .ccmr1 =
        {
            .in =
            {
                .bf =
                {
                    .cc1s   = 0x01,
                    .ic1psc = 0x00,
                    .ic1f   = 0x00,
                    .cc2s   = 0x01,
                    .ic2psc = 0x00,
                    .ic2f   = 0x00,
                },
            },
        },

        .ccmr2 =
        {
            .in =
            {
                .bf =
                {
                    .cc3s   = 0x01,
                    .ic3psc = 0x00,
                    .ic3f   = 0x00,
                    .cc4s   = 0x01,
                    .ic4psc = 0x00,
                    .ic4f   = 0x00,
                },
            },
        },

        .ccer =
        {
            .bf =
            {
                .cc1e  = 0x01,
                .cc1p  = 0x01,
                .cc1ne = 0x00,
                .cc1np = 0x01,
                .cc2e  = 0x01,
                .cc2p  = 0x01,
                .cc2ne = 0x00,
                .cc2np = 0x01,
                .cc3e  = 0x01,
                .cc3p  = 0x01,
                .cc3ne = 0x00,
                .cc3np = 0x01,
                .cc4e  = 0x01,
                .cc4p  = 0x01,
                .cc4np = 0x01,
                .cc5e  = 0x00,
                .cc5p  = 0x00,
                .cc6e  = 0x00,
                .cc6p  = 0x00,
            },
        },

        .cnt =
        {
            .bf =
            {
                .cnt    = 0x00,
                .uifcpy = 0x00,
            },
        },

        .psc =
        {
            .bf =
            {
                .psc = 0xd7,
            },
        },

        .arr =
        {
            .bf =
            {
                .arr = 0xffff,
            },
        },

        .rcr =
        {
            .bf =
            {
                .rep = 0x00,
            },
        },

        .ccr1 =
        {
            .bf =
            {
                .ccr1 = 0x00,
            },
        },

        .ccr2 =
        {
            .bf =
            {
                .ccr2 = 0x00,
            },
        },

        .ccr3 =
        {
            .bf =
            {
                .ccr3 = 0x00,
            },
        },

        .ccr4 =
        {
            .bf =
            {
                .ccr4 = 0x00,
            },
        },

        .bdtr =
        {
            .bf =
            {
                .dtg  = 0x00,
                .lock = 0x00,
                .ossi = 0x00,
                .ossr = 0x00,
                .bke  = 0x00,
                .bkp  = 0x00,
                .aoe  = 0x00,
                .moe  = 0x00,
                .bkf  = 0x00,
                .bk2f = 0x00,
                .bk2e = 0x00,
                .bk2p = 0x00,
            },
        },

        .dcr =
        {
            .bf =
            {
                .dba = 0x00,
                .dbl = 0x00,
            },
        },

        .dmar =
        {
            .bf =
            {
                .dmab = 0x00,
            },
        },

        .ccmr3 =
        {
            .bf =
            {
                .oc5fe    = 0x00,
                .oc5pe    = 0x00,
                .oc5m     = 0x00,
                .oc5ce    = 0x00,
                .oc6fe    = 0x00,
                .oc6pe    = 0x00,
                .oc6m     = 0x00,
                .oc6ce    = 0x00,
                .oc5m_msb = 0x00,
                .oc6m_msb = 0x00,
            },
        },

        .ccr5 =
        {
            .bf =
            {
                .ccr5  = 0x00,
                .gc5c1 = 0x00,
                .gc5c2 = 0x00,
                .gc5c3 = 0x00,
            },
        },

        .ccr6 =
        {
            .bf =
            {
                .ccr6 = 0x00,
            },
        },
    },
    .ccr_data   = { 0 },
    .id         = LL_TIM_ADV6_TIM18_ID_8,
    .ccmr1_mode = LL_TIM_ADV6_TIM18_MODE_IN_CAP,
    .ccmr2_mode = LL_TIM_ADV6_TIM18_MODE_IN_CAP,
    .stat       = false,
};

///
/// \brief The TIM devices array.
///
static struct tim_dev tim_dev_arr[TIM_INST_TOTAL] =
{
    [TIM_INST_4] =
    {
        .tim          = &tim4,
        .init         = &ll_tim_gpx_tim2345_init,
        .deinit       = &ll_tim_gpx_tim2345_deinit,
        .enable       = &ll_tim_gpx_tim2345_enable,
        .disable      = &ll_tim_gpx_tim2345_disable,
        .ccr_data_get = &ll_tim_gpx_tim2345_ccr_data_get,
        .ccr_set      = &ll_tim_gpx_tim2345_ccr_set,
    },

    [TIM_INST_12] =
    {
        .tim          = &tim12,
        .init         = &ll_tim_gpx_tim912_init,
        .deinit       = &ll_tim_gpx_tim912_deinit,
        .enable       = &ll_tim_gpx_tim912_enable,
        .disable      = &ll_tim_gpx_tim912_disable,
        .ccr_data_get = &ll_tim_gpx_tim912_ccr_data_get,
        .ccr_set      = &ll_tim_gpx_tim912_ccr_set,
    },

    [TIM_INST_8] =
    {
        .tim          = &tim8,
        .init         = &ll_tim_adv6_tim18_init,
        .deinit       = &ll_tim_adv6_tim18_deinit,
        .enable       = &ll_tim_adv6_tim18_enable,
        .disable      = &ll_tim_adv6_tim18_disable,
        .ccr_data_get = &ll_tim_adv6_tim18_ccr_data_get,
        .ccr_set      = &ll_tim_adv6_tim18_ccr_set,
    },
};

///***********************************************************************************************************
/// Global functions - definition.
///***********************************************************************************************************
void _tim8brktim12_handler(void)
{
    volatile struct ll_tim_gpx_tim912_dev *tim =
        (volatile struct ll_tim_gpx_tim912_dev *)tim_dev_arr[TIM_INST_12].tim;

    if (tim->rmap->sr.bf.cc1if)
    {
        uint16_t curr = tim->rmap->ccr1.bf.ccr1;

        tim->ccr_data[LL_TIM_CCR_CH1].prev = tim->ccr_data[LL_TIM_CCR_CH1].curr;
        tim->ccr_data[LL_TIM_CCR_CH1].curr = curr;
    }

    if (tim->rmap->sr.bf.cc2if)
    {
        uint16_t curr = tim->rmap->ccr2.bf.ccr2;

        tim->ccr_data[LL_TIM_CCR_CH2].prev = tim->ccr_data[LL_TIM_CCR_CH2].curr;
        tim->ccr_data[LL_TIM_CCR_CH2].curr = curr;
    }
}

void _tim8cc_handler(void)
{
    volatile struct ll_tim_adv6_tim18_dev *tim =
        (volatile struct ll_tim_adv6_tim18_dev *)tim_dev_arr[TIM_INST_8].tim;

    if (tim->rmap->sr.bf.cc1if)
    {
        uint16_t curr = tim->rmap->ccr1.bf.ccr1;

        tim->ccr_data[LL_TIM_CCR_CH1].prev = tim->ccr_data[LL_TIM_CCR_CH1].curr;
        tim->ccr_data[LL_TIM_CCR_CH1].curr = curr;
    }

    if (tim->rmap->sr.bf.cc2if)
    {
        uint16_t curr = tim->rmap->ccr2.bf.ccr2;

        tim->ccr_data[LL_TIM_CCR_CH2].prev = tim->ccr_data[LL_TIM_CCR_CH2].curr;
        tim->ccr_data[LL_TIM_CCR_CH2].curr = curr;
    }

    if (tim->rmap->sr.bf.cc3if)
    {
        uint16_t curr = tim->rmap->ccr3.bf.ccr3;

        tim->ccr_data[LL_TIM_CCR_CH3].prev = tim->ccr_data[LL_TIM_CCR_CH3].curr;
        tim->ccr_data[LL_TIM_CCR_CH3].curr = curr;
    }

    if (tim->rmap->sr.bf.cc4if)
    {
        uint16_t curr = tim->rmap->ccr4.bf.ccr4;

        tim->ccr_data[LL_TIM_CCR_CH4].prev = tim->ccr_data[LL_TIM_CCR_CH4].curr;
        tim->ccr_data[LL_TIM_CCR_CH4].curr = curr;
    }
}

struct tim_dev* tim_dev_get(tim_inst_t inst)
{
    if ((inst < TIM_INST_BEGIN) || (inst >= TIM_INST_TOTAL))
    {
        return NULL;
    }

    return &tim_dev_arr[inst];
}

struct tim_dev* tim_dev_arr_get(void)
{
    return &tim_dev_arr[0];
}

void tim_init(void)
{
    for (uint32_t i = 0; i < sizeof(tim_dev_arr)/sizeof(tim_dev_arr[TIM_INST_BEGIN]); i++)
    {
        tim_dev_arr[i].init(tim_dev_arr[i].tim);
        tim_dev_arr[i].enable(tim_dev_arr[i].tim);
    }
}
