PanBabinicz/ghost-feather/tests/gtest/controller/bmi270/acc_get_z/acc_get_z.cc

#include <gtest/gtest.h>
#include <stdint.h>
#include "bmi270.h"
#include "libopencm3/stm32/spi_common.h"

uint32_t      SPI_CR1_ARR[SPI_INTF_TOTAL];
uint32_t      SPI_CRCPR_ARR[SPI_INTF_TOTAL];
struct spi_dr SPI_DR_ARR[SPI_INTF_TOTAL];

///
/// \brief The gtest_bmi270_acc_get_z test fixture class.
///
class gtest_bmi270_acc_get_z : public ::testing::Test
{
    protected:
        static void SetUpTestSuite()
        {
            bmi270 = bmi270_dev_get();
        }

        static void TearDownTestSuite()
        {
            bmi270 = nullptr;
        }

        void SetUp() override
        {
            if (::testing::UnitTest::GetInstance()->current_test_info()->name() ==
                std::string("procedure"))
            {
                int16_t z = 0xc0de;
                (void)bmi270_acc_set_z(bmi270, z);
            }
        }

        void TearDown() override
        {
            if (::testing::UnitTest::GetInstance()->current_test_info()->name() ==
                std::string("procedure"))
            {
                int16_t z = 0x0000;
                (void)bmi270_acc_set_z(bmi270, z);
            }
        }

        static bmi270_dev *bmi270;
};

struct bmi270_dev *gtest_bmi270_acc_get_z::bmi270 = nullptr;

///
/// \brief This test performs the bmi270 accelerometer get z axis procedure.
///
TEST_F(gtest_bmi270_acc_get_z, procedure)
{
    bmi270_res_t res;
    int16_t z;

    res = bmi270_acc_get_z(gtest_bmi270_acc_get_z::bmi270, &z);
    EXPECT_EQ(res, BMI270_RES_OK);

    EXPECT_EQ(z, (int16_t)0xc0de);
}

///
/// \brief This test checks the null pointer protection inside bmi270 accelerometer
///        get z function.
///
TEST_F(gtest_bmi270_acc_get_z, null_pointer_protection)
{
    bmi270_res_t res;
    int16_t z;

    res = bmi270_acc_get_z(NULL, &z);
    EXPECT_EQ(res, BMI270_RES_ERR);

    res = bmi270_acc_get_z(gtest_bmi270_acc_get_z::bmi270, NULL);
    EXPECT_EQ(res, BMI270_RES_ERR);
}
